bajraan/PRT_ATHIQ_BQ24072_DevBoard/21_Electrical/00__Screens_1/Screenshot (2036).png

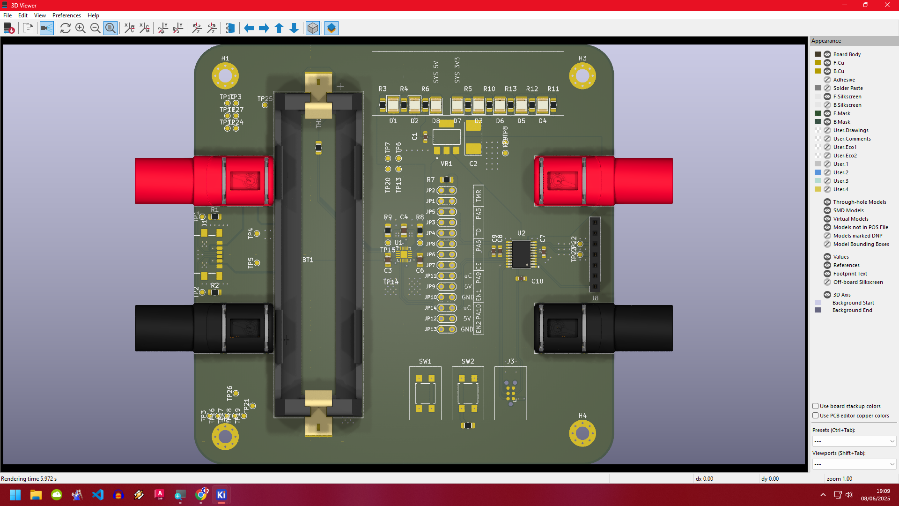
21_Electrical/00__Screens_1/Screenshot (2036).png
